Expatria-Technologies/Mods-Accessories/Expatria/Jog2K_Base/6mm_button.SLDPRT

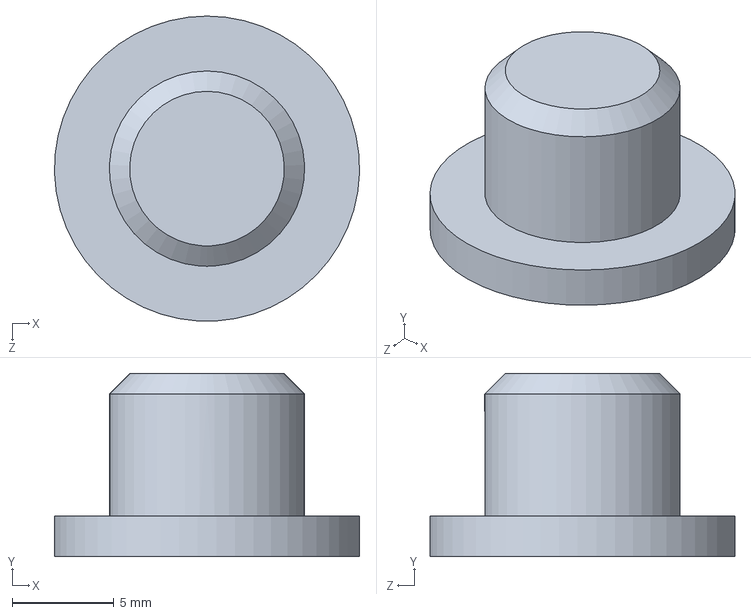
[picture p36: CAD file, 2023-01-20]
Expatria/Jog2K_Base/6mm_button.SLDPRT
15.0 x 9.00 x 15.0 mm
