Expatria-Technologies/Mods-Accessories/Expatria/Jog2K_Deluxe/Buttons/Black/Start Button Cover.stl

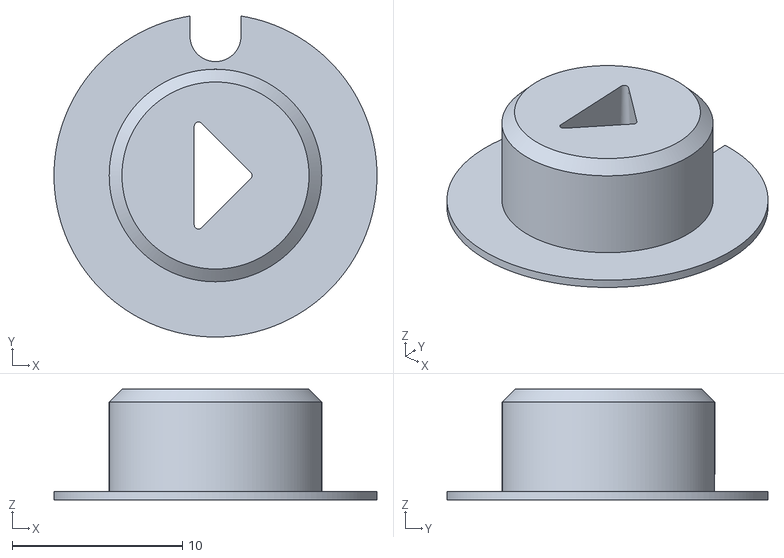
[picture p37: CAD file, 2023-01-20]
Expatria/Jog2K_Deluxe/Buttons/Black/Start Button Cover.stl
19.0 x 18.9 x 6.50
