Expatria-Technologies/Mods-Accessories/Expatria/Jog2K_Deluxe/Buttons/Translucent/Raise Button Lightpipe x2.stl

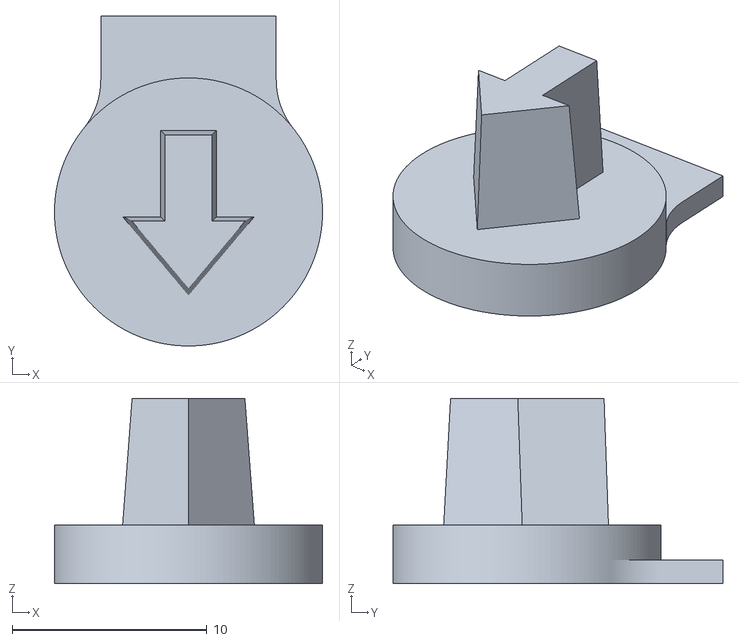
[picture p38: CAD file, 2023-01-20]
Expatria/Jog2K_Deluxe/Buttons/Translucent/Raise Button Lightpipe x2.stl
13.8 x 16.9 x 9.50
