Expatria-Technologies/Mods-Accessories/Expatria/Jog2K_Deluxe/Buttons/White/Mist Button Core.stl

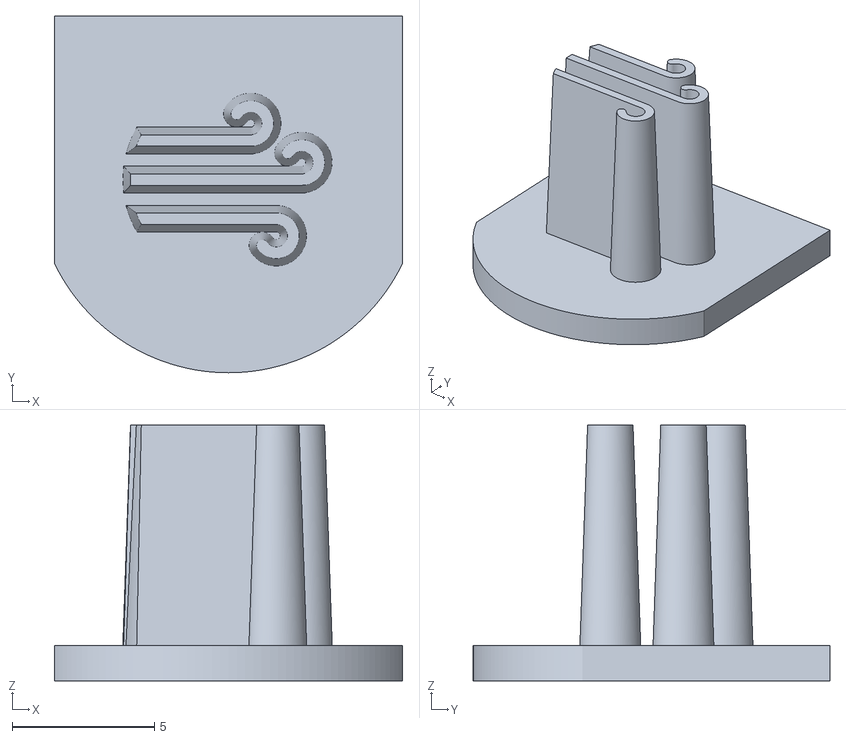
[picture p39: CAD file, 2023-01-20]
Expatria/Jog2K_Deluxe/Buttons/White/Mist Button Core.stl
12.2 x 12.6 x 9.00
