Expatria-Technologies/Mods-Accessories/Expatria/Jog2K_Deluxe/Enclosure/1.3in - Top Cover.STL

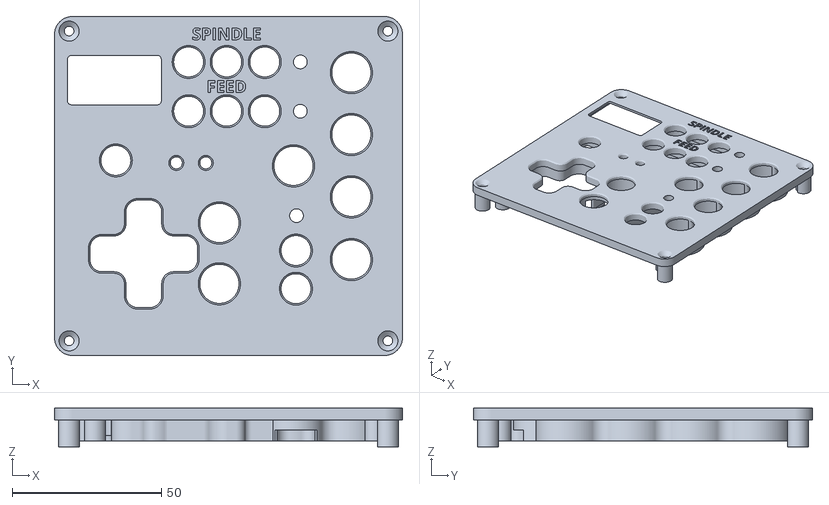
[picture p40: CAD file, 2023-03-23]
Expatria/Jog2K_Deluxe/Enclosure/1.3in - Top Cover.STL
116.5 x 113.5 x 13.0
