Expatria-Technologies/Mods-Accessories/Expatria/Jog2K_Deluxe/Src/0.96in - Jog2K Deluxe Edition.step

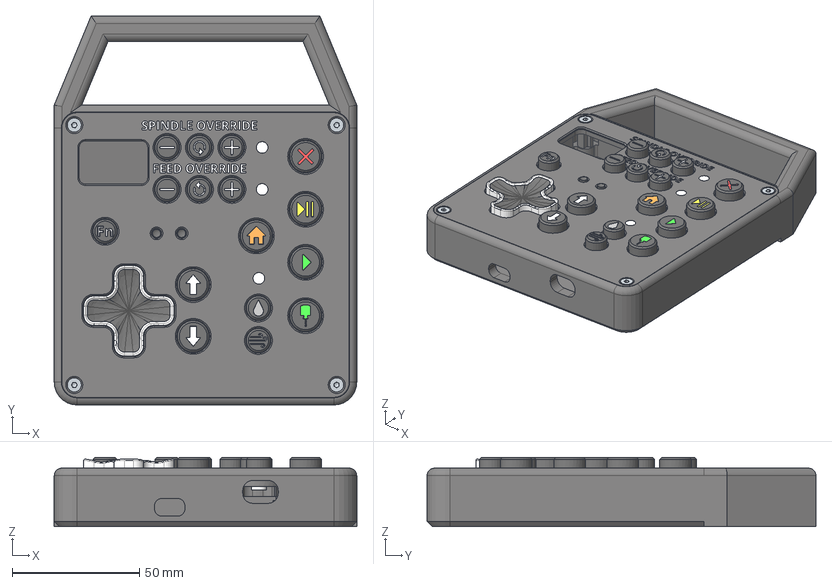
[picture p41: CAD file, 2023-01-22]
Expatria/Jog2K_Deluxe/Src/0.96in - Jog2K Deluxe Edition.step
119.0 x 153.0 x 27.2 mm
Lightpipe x 3
Start Button Cover
Reset Button Core x 2
D-Pad Lower
Spindle Button Lightpipe
Home Button Cover
Hex socket head cap screw M3x0.50 x 6 x 7
Hex socket countersunk head screw M3x0.5 x 16 x 4
Flood Button Cover
Raise Button Lightpipe x 2
Start Button Lightpipe
D-Pad Upper
Plus Button Core x 2
Top Cover
Minus Button Cover x 2
Mist Button Core
Halt Button Lightpipe
Mist Button Cover
Hold Button Lightpipe
Reset Button Cover x 2
Minus Button Core x 2
Plus Button Cover x 2
Fn Button Core
Spindle Button Cover
4mm Button Short x 2
Flood Button Core
Bottom Enclosure
Hold Button Cover
Window
Fn Button Cover
Raise Button Cover x 2
Home Button Lightpipe
Halt Button Cover
