Expatria-Technologies/Mods-Accessories/Expatria/Limit_PCB_Case/Limit Breakout Case Lid.stl

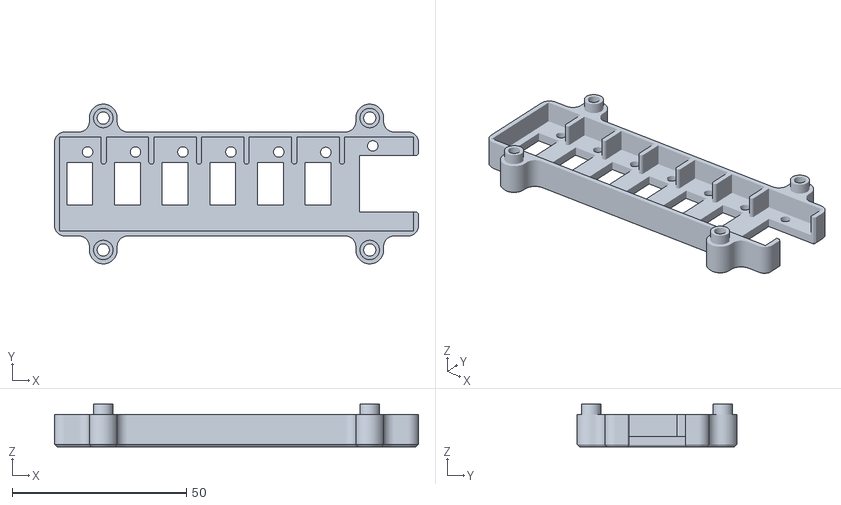
[picture p42: CAD file, 2023-01-20]
Expatria/Limit_PCB_Case/Limit Breakout Case Lid.stl
104.5 x 45.9 x 12.3
