Expatria-Technologies/Mods-Accessories/Community_Submissions/Button_PCB_Case/Button Breakout Case v2.step

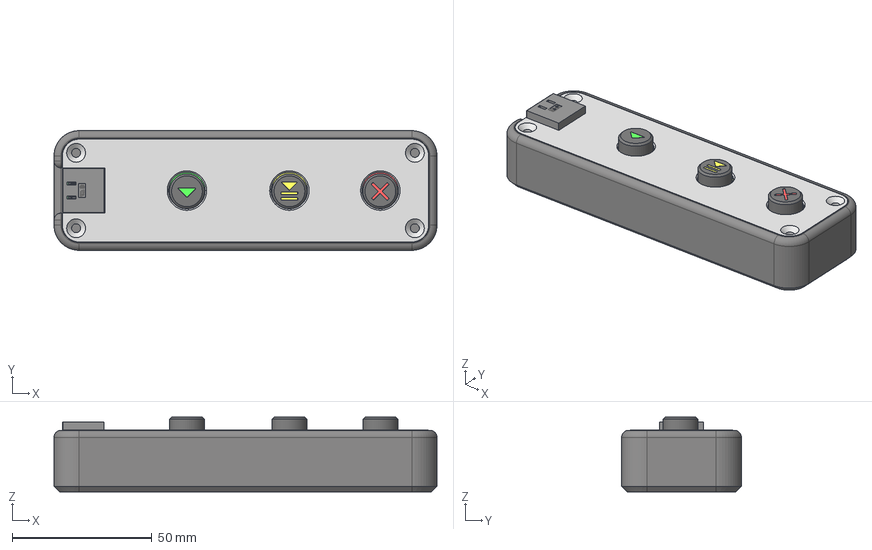
[picture p43: CAD file, 2023-01-20]
Community_Submissions/Button_PCB_Case/Button Breakout Case v2.step
136.9 x 42.8 x 26.7 mm
Conn_Amphenol_RJHSE-5080_eec
c-4-1437565-2-s-3d x 3
User_Library-RES_1609-0603 x 7
User_Library-LED_0603_R_Pocket002 (1) x 4
User_Library-LED_0603_R_Pad004 (1) x 4
User_Library-LED_0603_R_Fillet (1) x 4
User_Library-LED_0603_R_Pocket001 (1) x 4
User_Library-LED_0603_R_Pad (1) x 4
J26 x 4
Top Cover Button Breakout
Bottom Button Breakout Enclosure
Halt Button Cover
Start Button Cover
Start Button Lightpipe
Hold Button Cover
Hold Button Lightpipe
Halt Button Lightpipe
