Expatria-Technologies/Mods-Accessories/Community_Submissions/FDM_Buttons/Black/Home Button Cover.stl

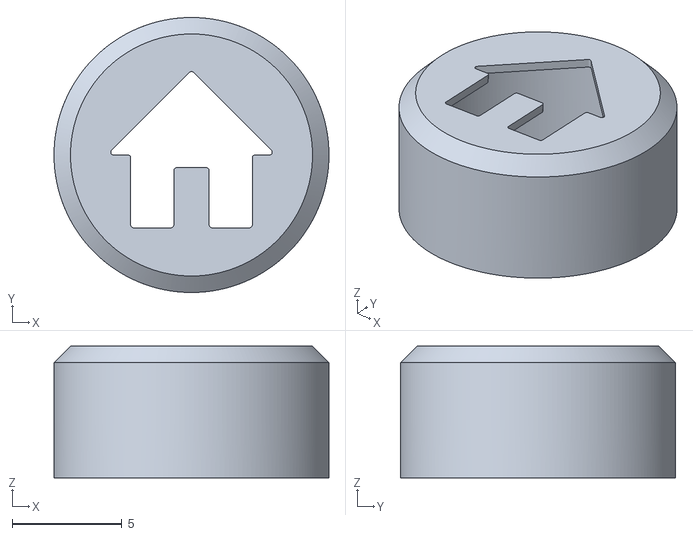
[picture p44: CAD file, 2023-01-20]
Community_Submissions/FDM_Buttons/Black/Home Button Cover.stl
12.5 x 12.5 x 6.00
