Expatria-Technologies/Mods-Accessories/Community_Submissions/FDM_Buttons/Translucent/Z Button Lightpipe 2x.stl

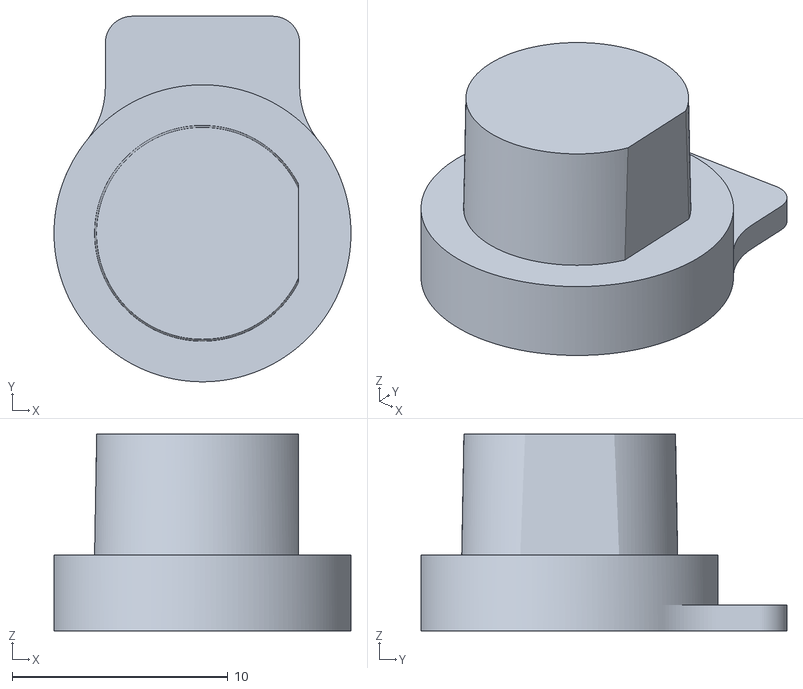
[picture p45: CAD file, 2023-01-20]
Community_Submissions/FDM_Buttons/Translucent/Z Button Lightpipe 2x.stl
13.8 x 16.9 x 9.10
