Expatria-Technologies/Mods-Accessories/Community_Submissions/FDM_Buttons/White/Override Button Core 6x.stl

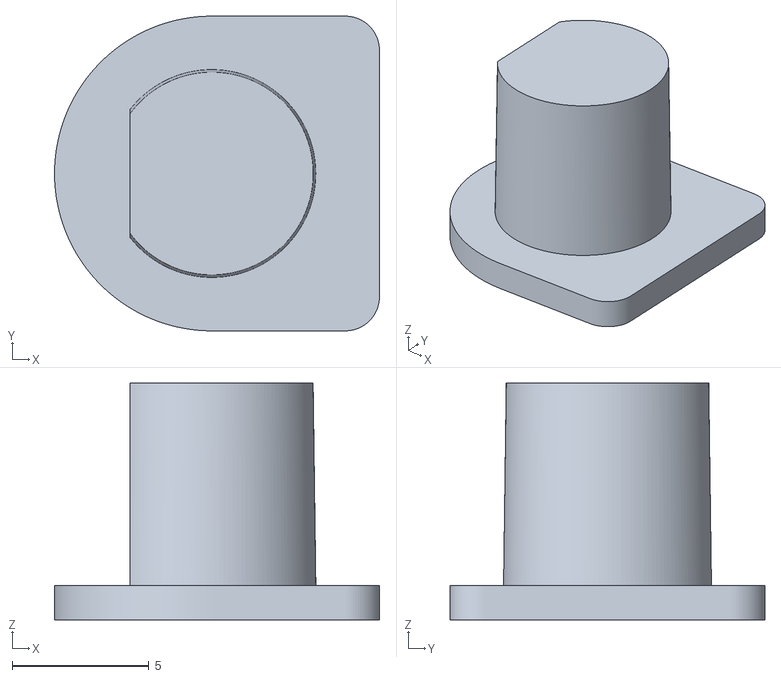
[picture p46: CAD file, 2023-01-20]
Community_Submissions/FDM_Buttons/White/Override Button Core 6x.stl
11.9 x 11.5 x 8.65
