Expatria-Technologies/Mods-Accessories/Community_Submissions/FLEXI_HAL_PI_DIN_RAIL_MOUNT/STL/M2 Spacer 11mm.stl

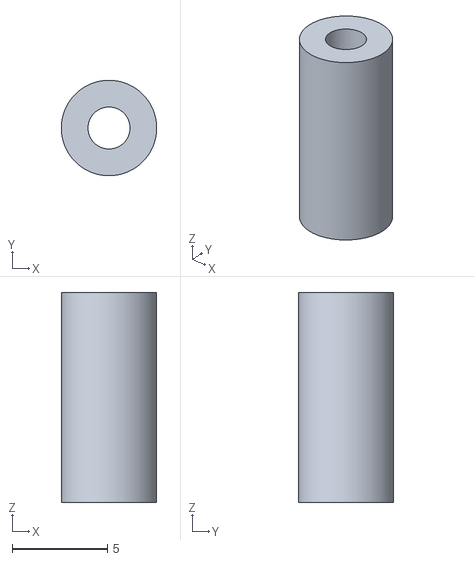
[picture p47: CAD file, 2024-12-16]
Community_Submissions/FLEXI_HAL_PI_DIN_RAIL_MOUNT/STL/M2 Spacer 11mm.stl
5.00 x 5.00 x 11.0
