Expatria-Technologies/Mods-Accessories/Community_Submissions/GH2K_PCB_Mounting_Plate/GH2k or Relay Din Clamp 2x.stl

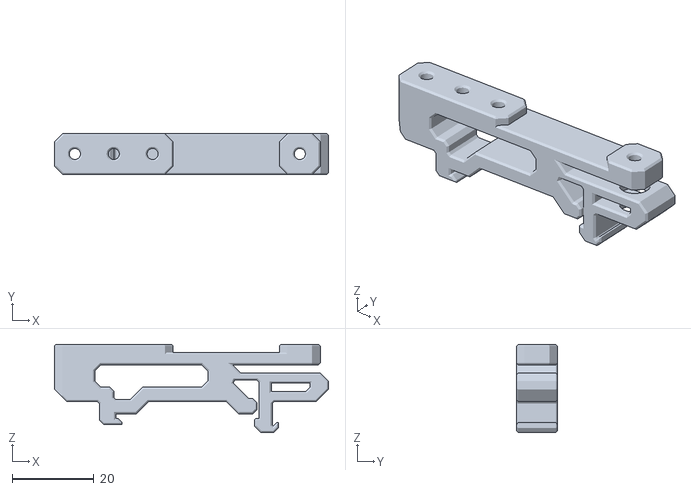
[picture p48: CAD file, 2023-01-20]
Community_Submissions/GH2K_PCB_Mounting_Plate/GH2k or Relay Din Clamp 2x.stl
67.0 x 10.00 x 21.6
