Expatria-Technologies/Mods-Accessories/Community_Submissions/Jog2K_Heavy_Case/CAD/case_front.step

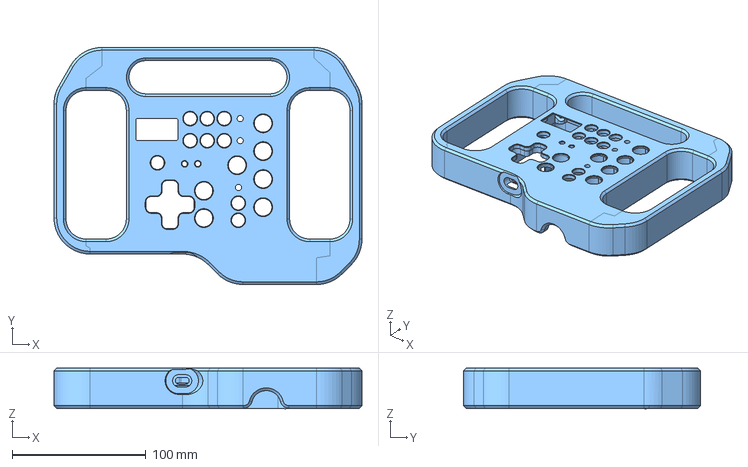
[picture p49: CAD file, 2025-08-29]
Community_Submissions/Jog2K_Heavy_Case/CAD/case_front.step
230.0 x 177.0 x 30.5 mm
