Expatria-Technologies/Mods-Accessories/Community_Submissions/Simplified_High_Vis_Buttons/Coolant.stl

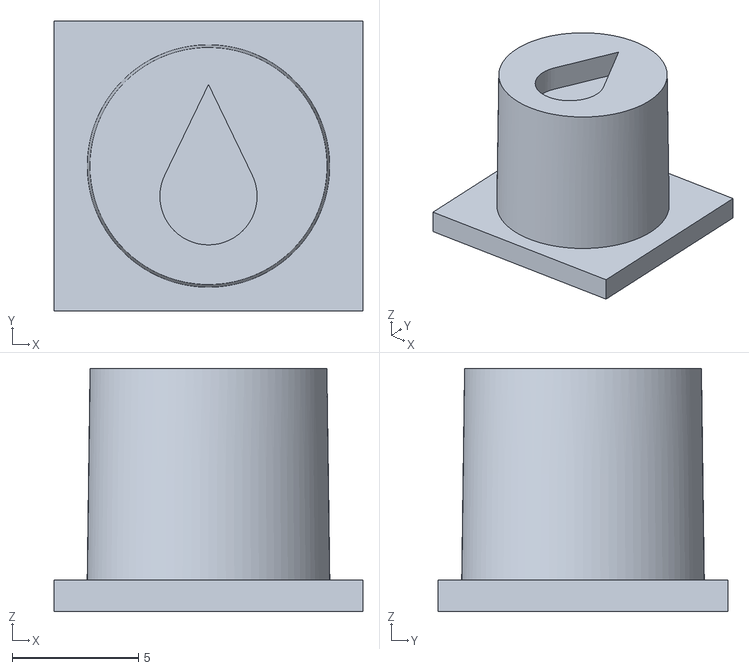
[picture p50: CAD file, 2023-01-22]
Community_Submissions/Simplified_High_Vis_Buttons/Coolant.stl
12.2 x 11.5 x 9.65
