Expatria-Technologies/Mods-Accessories/Expatria/Encoder_MK2_Case/encoderMK2_Enclosure_bottom.STEP

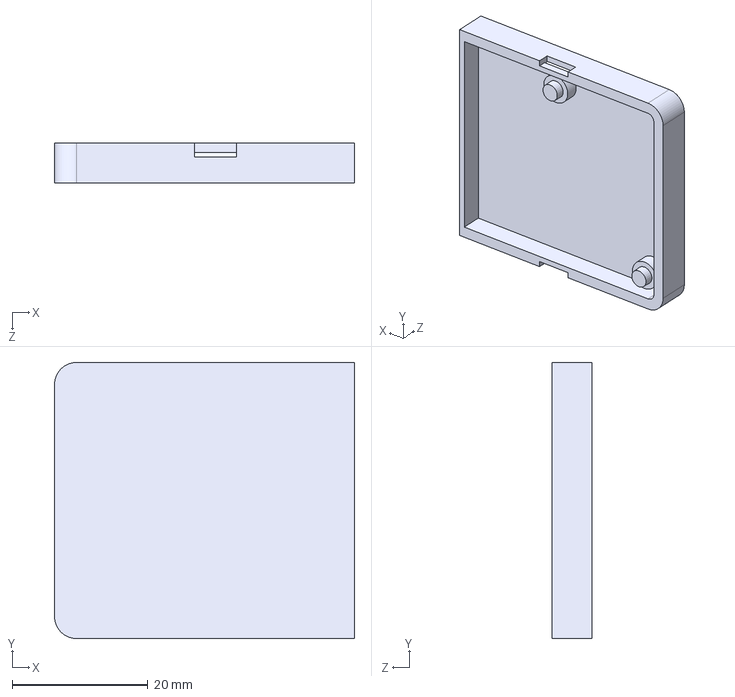
[picture p51: CAD file, 2024-12-16]
Expatria/Encoder_MK2_Case/encoderMK2_Enclosure_bottom.STEP
44.1 x 40.6 x 5.90 mm
