Expatria-Technologies/Mods-Accessories/Expatria/Jog2K_Base/jog_bottom_box_slim.SLDPRT

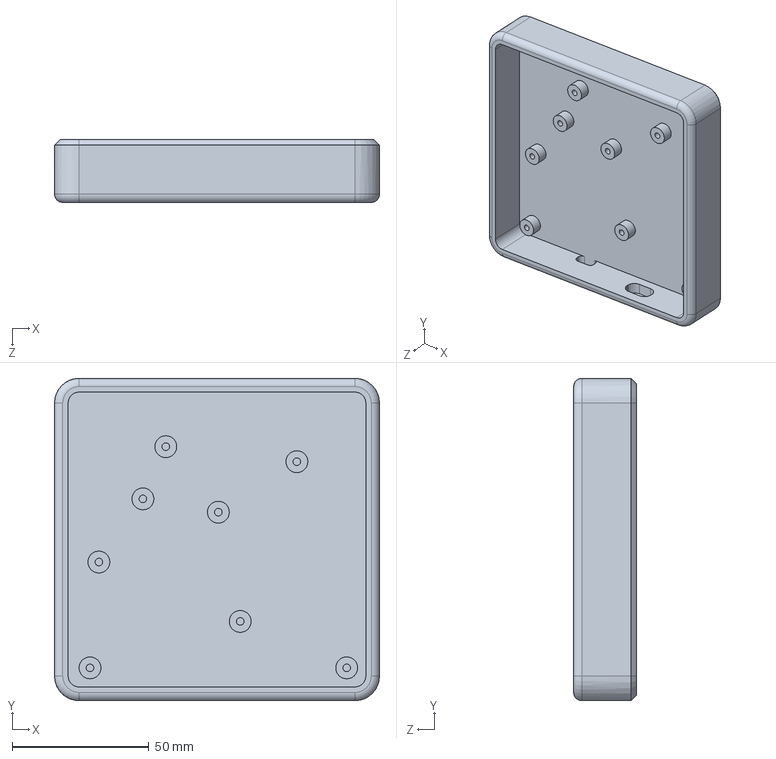
[picture p52: CAD file, 2023-01-20]
Expatria/Jog2K_Base/jog_bottom_box_slim.SLDPRT
119.0 x 118.0 x 23.0 mm
