Expatria-Technologies/Mods-Accessories/Expatria/Jog2K_Deluxe/Buttons/White/Reset Button Core x2.stl

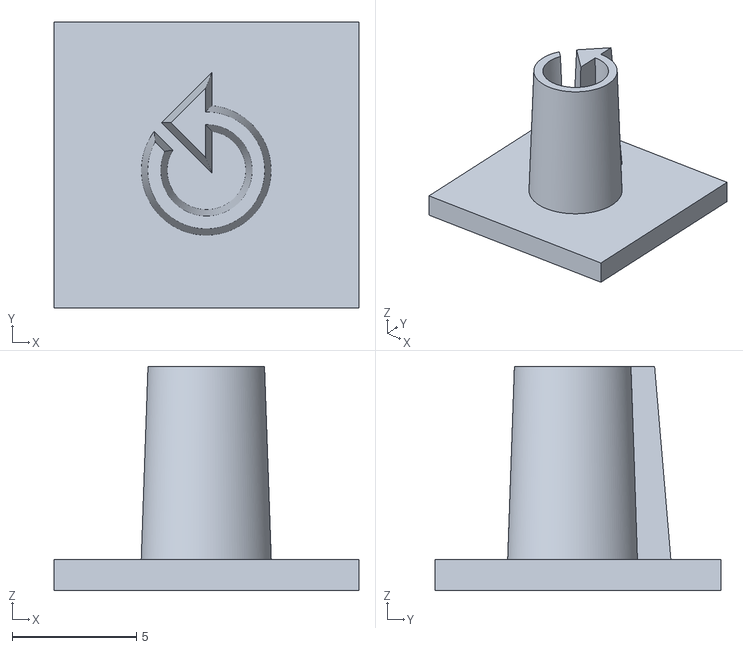
[picture p55: CAD file, 2023-01-20]
Expatria/Jog2K_Deluxe/Buttons/White/Reset Button Core x2.stl
12.2 x 11.5 x 9.00
