Expatria-Technologies/Mods-Accessories/Expatria/Jog2K_Deluxe/Enclosure/Slim - 1.3in Display Insert.stl

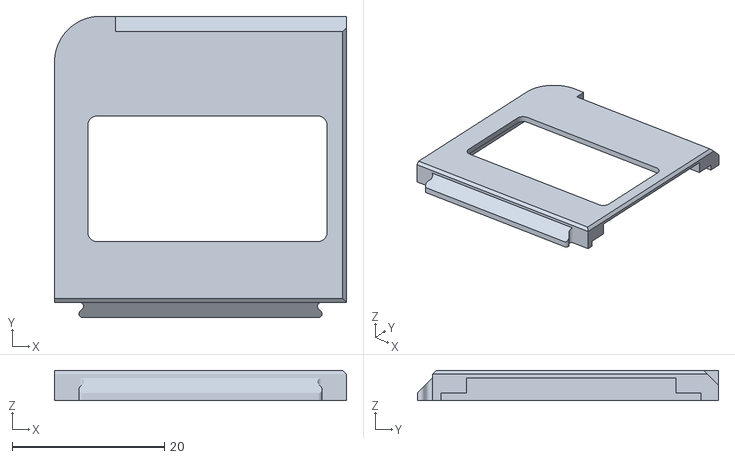
[picture p56: CAD file, 2023-02-04]
Expatria/Jog2K_Deluxe/Enclosure/Slim - 1.3in Display Insert.stl
38.3 x 39.5 x 4.00
