Expatria-Technologies/Mods-Accessories/Expatria/Limit_PCB_Case/Limit Breakout Case Base.stl

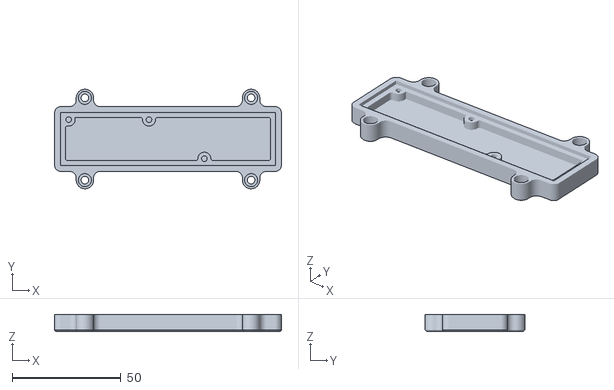
[picture p57: CAD file, 2023-01-20]
Expatria/Limit_PCB_Case/Limit Breakout Case Base.stl
104.5 x 45.9 x 8.00
