Expatria-Technologies/Mods-Accessories/Community_Submissions/Button_PCB_Case/Button PCB Case Cover.stl

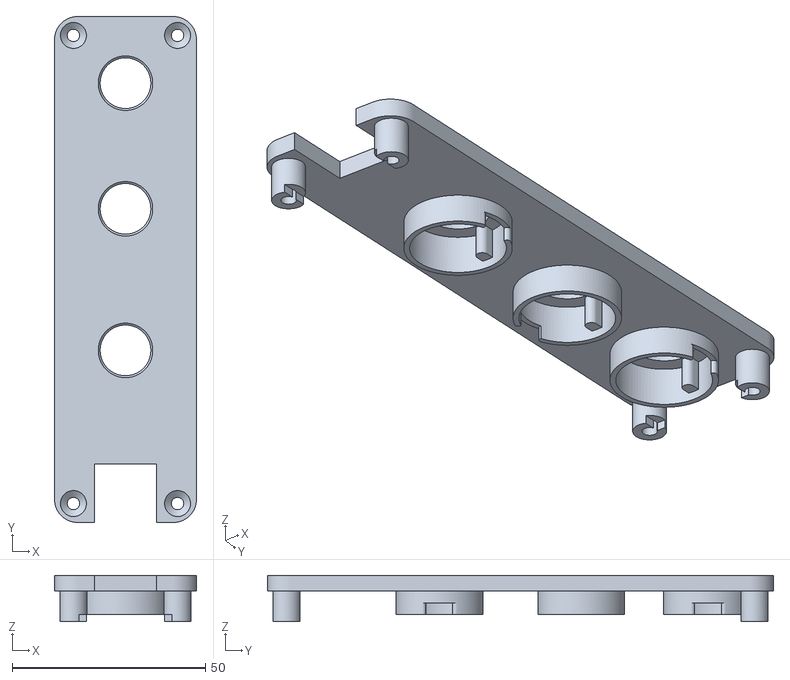
[picture p58: CAD file, 2023-01-20]
Community_Submissions/Button_PCB_Case/Button PCB Case Cover.stl
36.8 x 130.9 x 12.0
