Expatria-Technologies/Mods-Accessories/Community_Submissions/Button_PCB_Case/FDM Buttons/Black/Hold Button Cover.stl

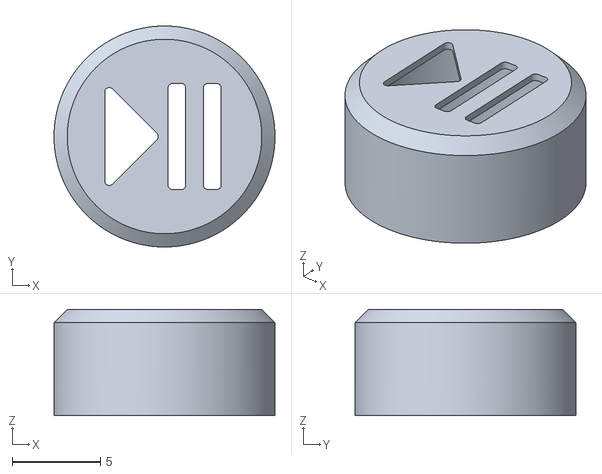
[picture p59: CAD file, 2023-01-20]
Community_Submissions/Button_PCB_Case/FDM Buttons/Black/Hold Button Cover.stl
12.5 x 12.5 x 6.00
