Expatria-Technologies/Mods-Accessories/Community_Submissions/FDM_Buttons/Black/Raise Button Cover 2x.stl

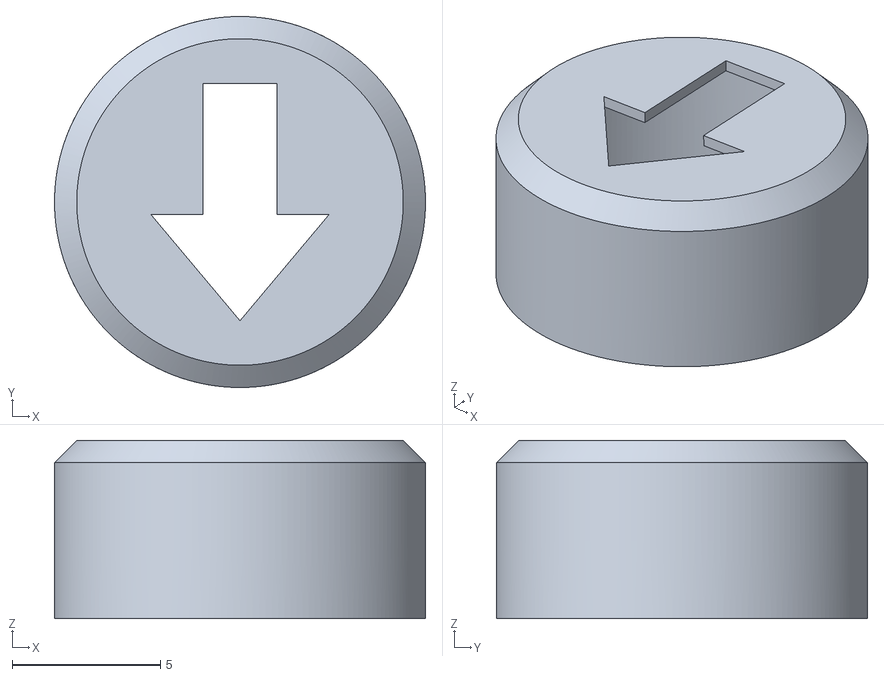
[picture p60: CAD file, 2023-01-20]
Community_Submissions/FDM_Buttons/Black/Raise Button Cover 2x.stl
12.5 x 12.5 x 6.00
