Expatria-Technologies/Mods-Accessories/Community_Submissions/FDM_Buttons/Translucent/Lightpipe x3.stl

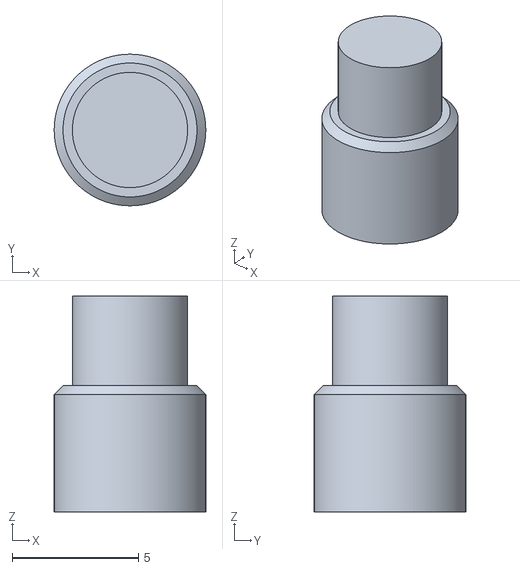
[picture p61: CAD file, 2023-01-20]
Community_Submissions/FDM_Buttons/Translucent/Lightpipe x3.stl
6.00 x 6.00 x 8.55
