Expatria-Technologies/Mods-Accessories/Community_Submissions/FLEXI_HAL_PI_DIN_RAIL_MOUNT/STL/DIN_Clip.stl

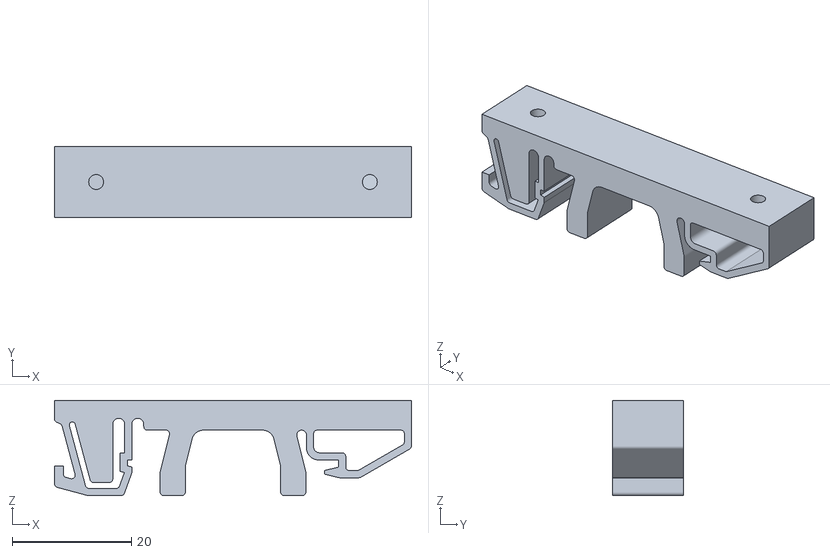
[picture p62: CAD file, 2023-01-20]
Community_Submissions/FLEXI_HAL_PI_DIN_RAIL_MOUNT/STL/DIN_Clip.stl
60.0 x 12.0 x 16.0
