Expatria-Technologies/Mods-Accessories/Community_Submissions/GH2K_PCB_Mounting_Plate/GH2K DIN Mounting Plate.stl

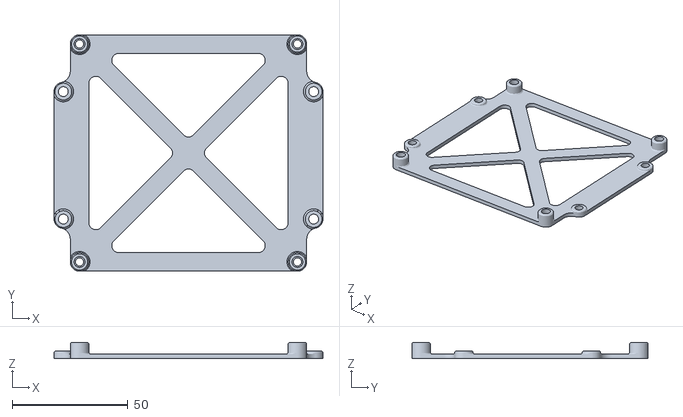
[picture p63: CAD file, 2023-01-20]
Community_Submissions/GH2K_PCB_Mounting_Plate/GH2K DIN Mounting Plate.stl
116.1 x 102.0 x 7.00
