Expatria-Technologies/Mods-Accessories/Community_Submissions/Simplified_High_Vis_Buttons/PlusOverrideX2.stl

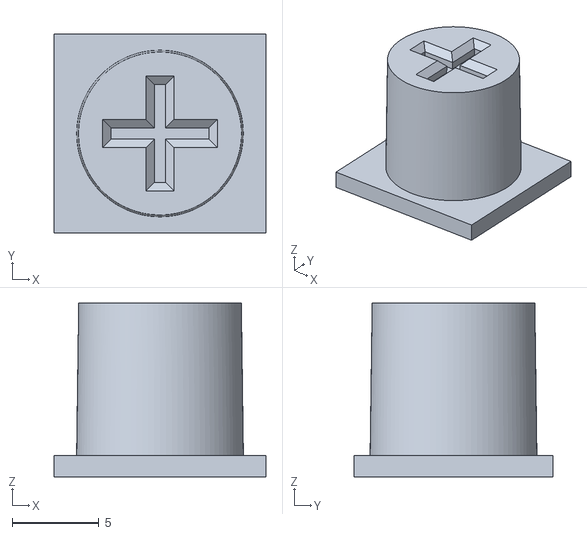
[picture p64: CAD file, 2023-01-22]
Community_Submissions/Simplified_High_Vis_Buttons/PlusOverrideX2.stl
12.2 x 11.5 x 10.0
