Expatria-Technologies/Mods-Accessories/Expatria/Jog2K_Deluxe/Buttons/Black/Mist Button Cover.stl

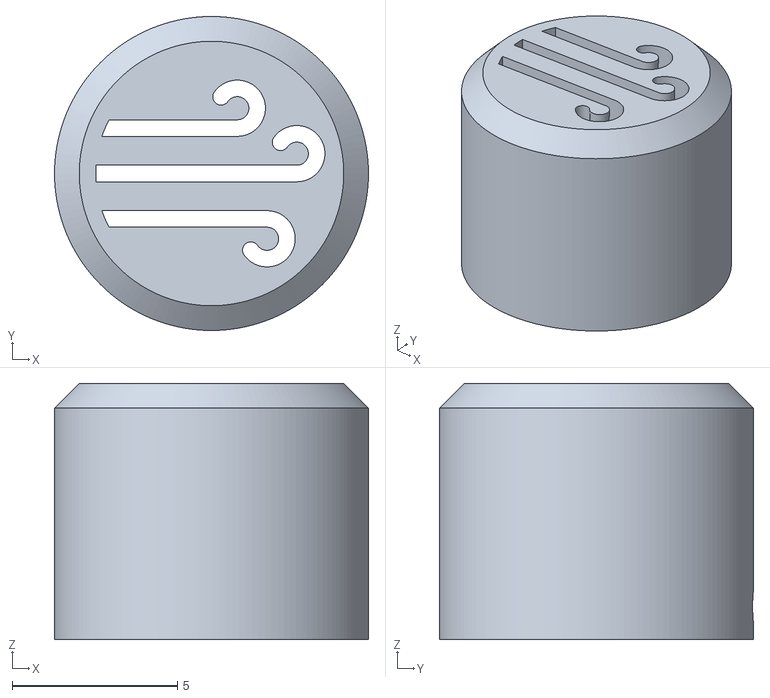
[picture p65: CAD file, 2023-01-20]
Expatria/Jog2K_Deluxe/Buttons/Black/Mist Button Cover.stl
9.50 x 9.50 x 7.75
