Expatria-Technologies/Mods-Accessories/Expatria/Jog2K_Deluxe/Enclosure/Slim - Blank Display Insert.stl

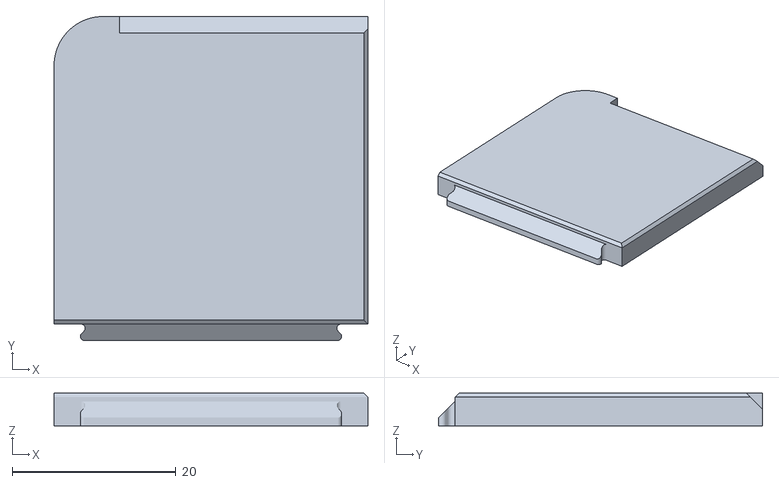
[picture p67: CAD file, 2023-02-04]
Expatria/Jog2K_Deluxe/Enclosure/Slim - Blank Display Insert.stl
38.3 x 39.5 x 4.00
