Expatria-Technologies/Mods-Accessories/Expatria/Limit_PCB_Case/Limit Breakout Lightpipe x7.stl

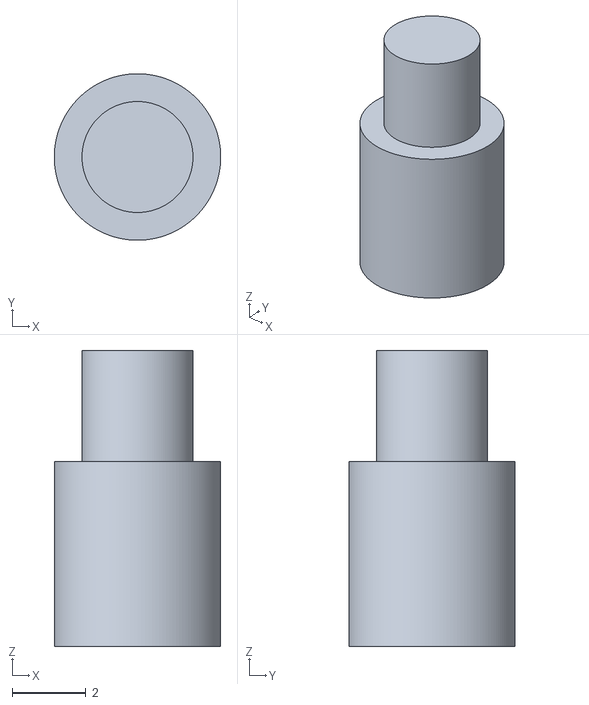
[picture p68: CAD file, 2023-01-20]
Expatria/Limit_PCB_Case/Limit Breakout Lightpipe x7.stl
4.50 x 4.50 x 8.00
