Expatria-Technologies/Mods-Accessories/Community_Submissions/FDM_Buttons/Black/Reset Button Cover 2x.stl

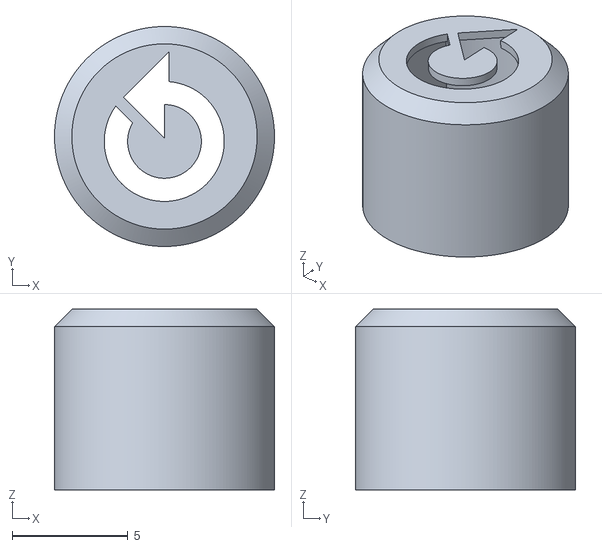
[picture p69: CAD file, 2023-01-20]
Community_Submissions/FDM_Buttons/Black/Reset Button Cover 2x.stl
9.50 x 9.50 x 7.80
