Expatria-Technologies/Mods-Accessories/Community_Submissions/Simplified_High_Vis_Buttons/Wind.stl

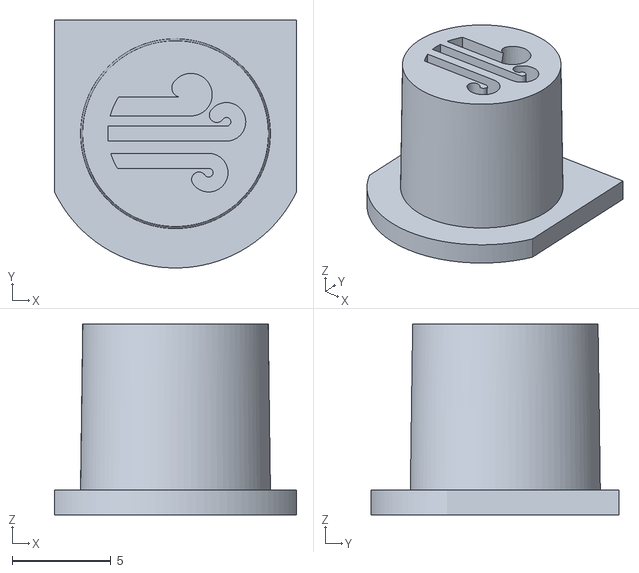
[picture p70: CAD file, 2023-01-22]
Community_Submissions/Simplified_High_Vis_Buttons/Wind.stl
12.2 x 12.5 x 9.65
