Expatria-Technologies/Mods-Accessories/Expatria/Jog2K_Base/10mm_button.SLDPRT

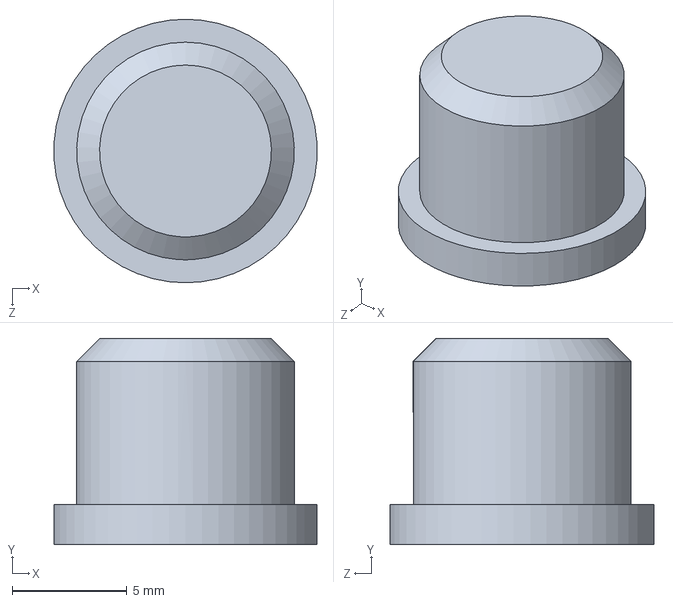
[picture p71: CAD file, 2023-01-20]
Expatria/Jog2K_Base/10mm_button.SLDPRT
11.5 x 9.00 x 11.5 mm
