Expatria-Technologies/Mods-Accessories/Expatria/Jog2K_Deluxe/Buttons/White/Minus Button Core x2.stl

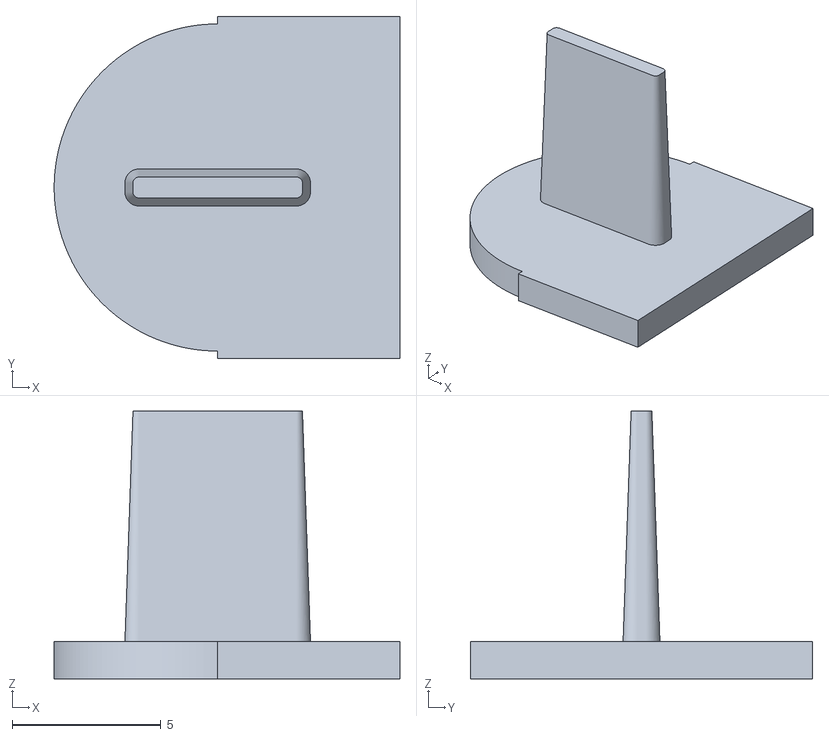
[picture p74: CAD file, 2023-01-20]
Expatria/Jog2K_Deluxe/Buttons/White/Minus Button Core x2.stl
11.6 x 11.5 x 9.00
