Expatria-Technologies/Mods-Accessories/Expatria/Jog2K_Deluxe/Enclosure/Slim - Top Cover.stl

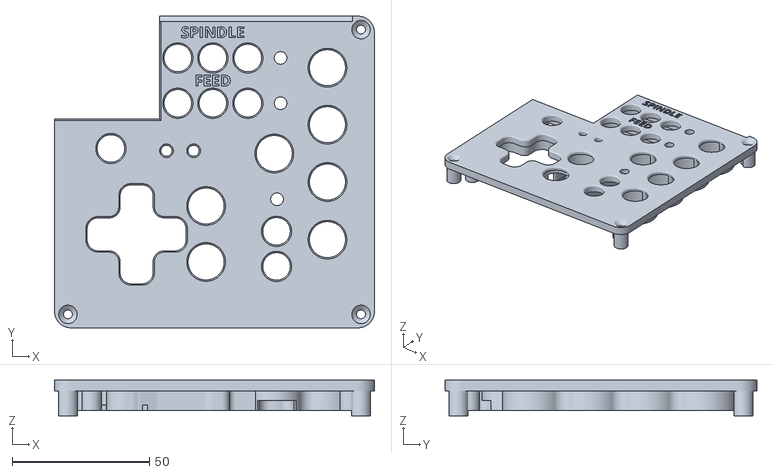
[picture p75: CAD file, 2023-02-04]
Expatria/Jog2K_Deluxe/Enclosure/Slim - Top Cover.stl
116.5 x 113.5 x 13.0
