Expatria-Technologies/Mods-Accessories/Community_Submissions/Simplified_High_Vis_Buttons/FnButton.stl

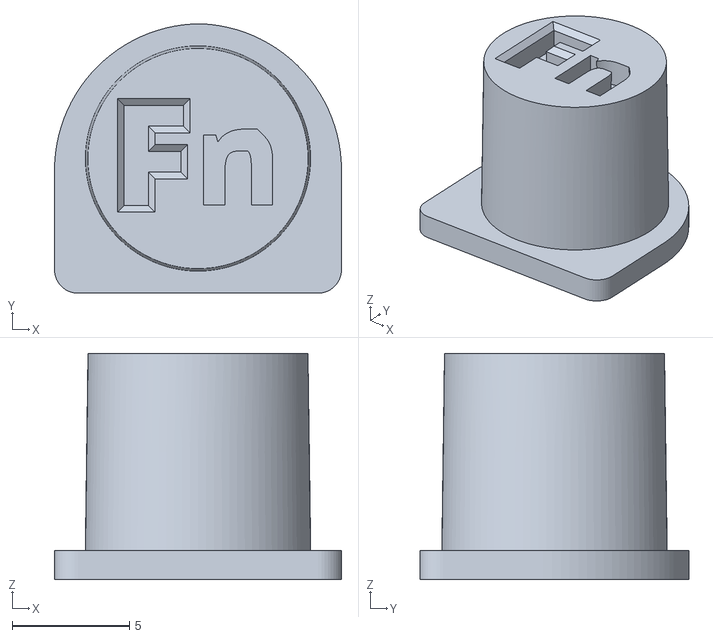
[picture p76: CAD file, 2023-01-22]
Community_Submissions/Simplified_High_Vis_Buttons/FnButton.stl
12.2 x 11.5 x 9.65
