Expatria-Technologies/Mods-Accessories/Expatria/Jog2K_Base/TopCover.SLDPRT

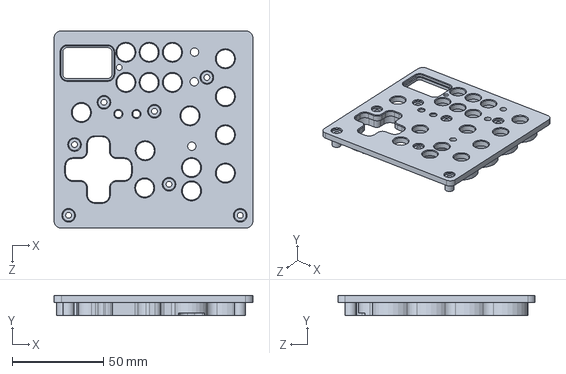
[picture p77: CAD file, 2023-01-20]
Expatria/Jog2K_Base/TopCover.SLDPRT
109.0 x 11.1 x 108.0 mm
