Expatria-Technologies/Mods-Accessories/Expatria/Jog2K_Deluxe/Buttons/Black/Reset Button Cover x2.stl

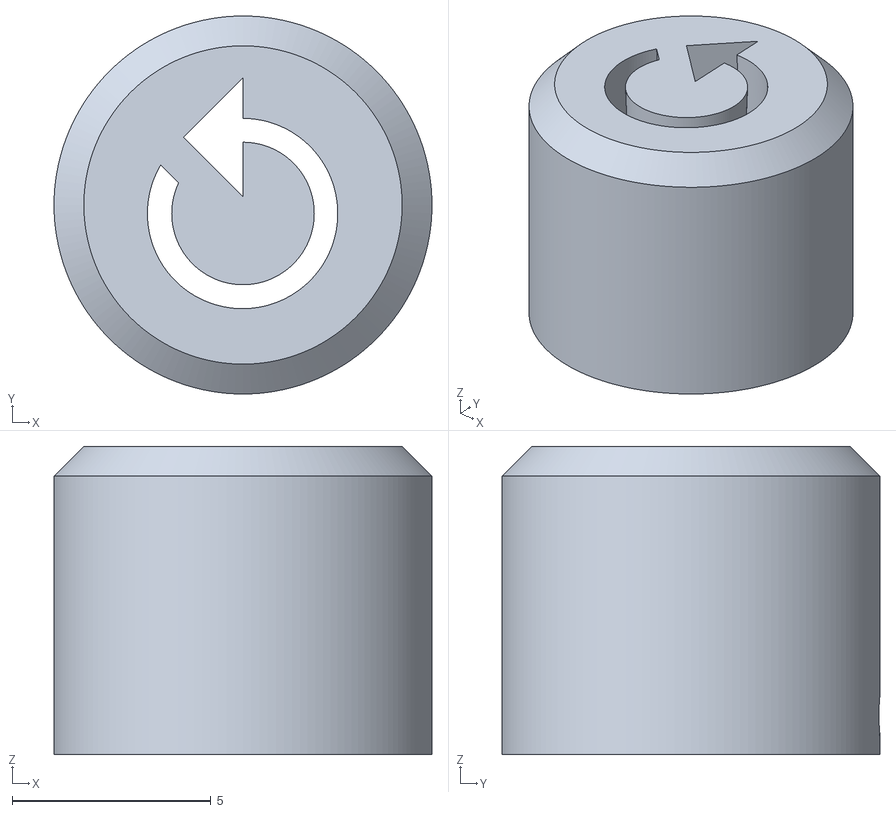
[picture p78: CAD file, 2023-01-20]
Expatria/Jog2K_Deluxe/Buttons/Black/Reset Button Cover x2.stl
9.50 x 9.50 x 7.75
