Expatria-Technologies/Mods-Accessories/Expatria/Jog2K_Deluxe/Buttons/Translucent/Hold Button Lightpipe.stl

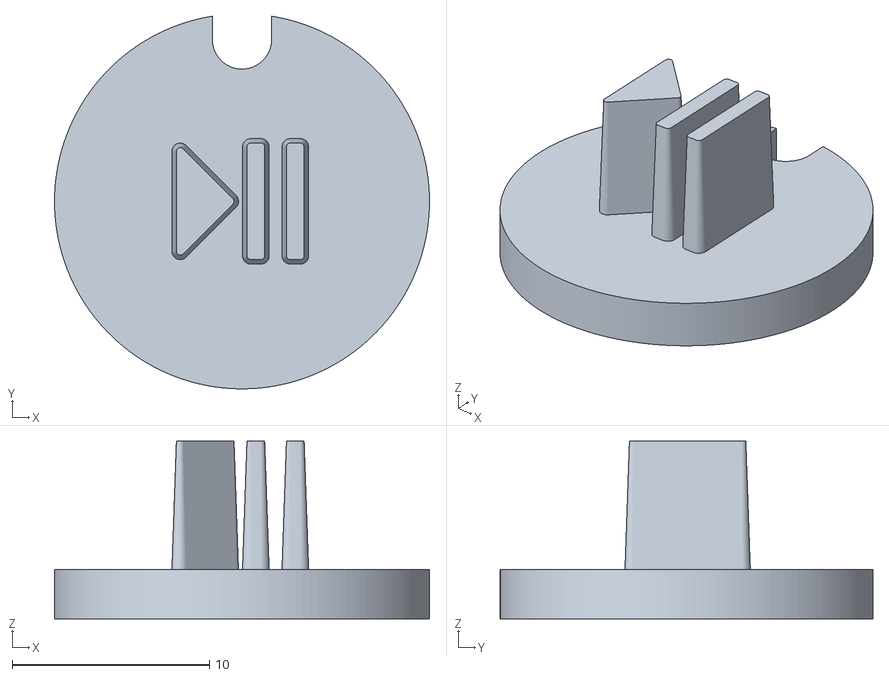
[picture p79: CAD file, 2023-01-20]
Expatria/Jog2K_Deluxe/Buttons/Translucent/Hold Button Lightpipe.stl
19.0 x 18.9 x 9.00
