Expatria-Technologies/Mods-Accessories/Expatria/Jog2K_Deluxe/Enclosure/Slim - Bottom Enclosure.stl

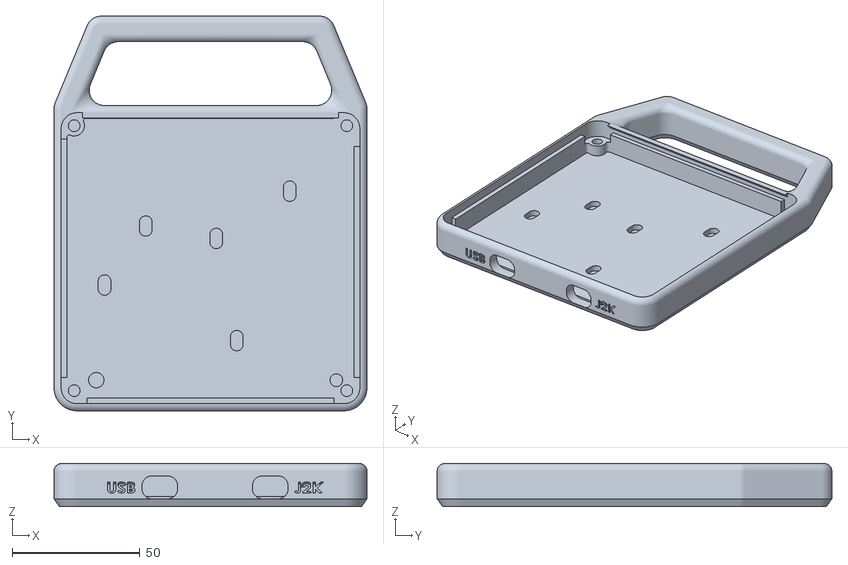
[picture p81: CAD file, 2023-02-04]
Expatria/Jog2K_Deluxe/Enclosure/Slim - Bottom Enclosure.stl
122.6 x 154.5 x 16.9
