Expatria-Technologies/Mods-Accessories/Community_Submissions/FDM_Buttons/Black/MicroUSBFiller.stl

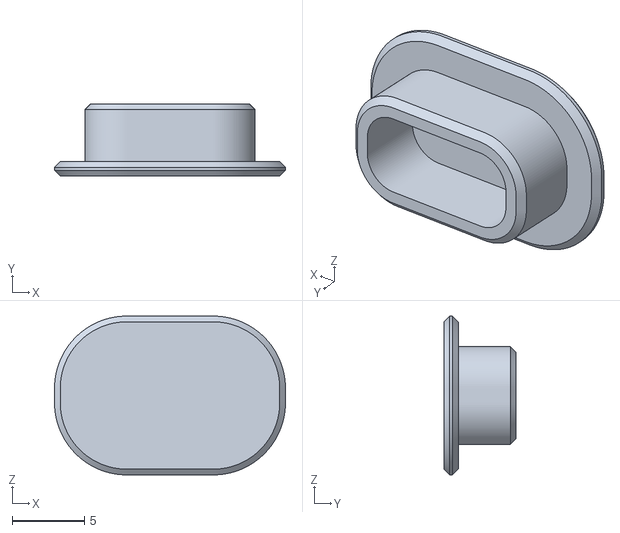
[picture p82: CAD file, 2023-01-20]
Community_Submissions/FDM_Buttons/Black/MicroUSBFiller.stl
16.0 x 5.00 x 11.0
