Expatria-Technologies/Mods-Accessories/Community_Submissions/Simplified_High_Vis_Buttons/MinusOverrideX2.stl

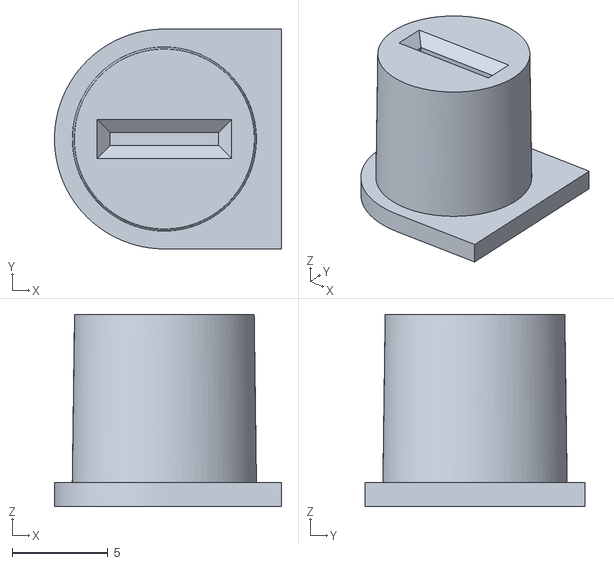
[picture p83: CAD file, 2023-01-22]
Community_Submissions/Simplified_High_Vis_Buttons/MinusOverrideX2.stl
11.9 x 11.5 x 10.0
