Expatria-Technologies/Mods-Accessories/Expatria/Jog2K_Deluxe/Buttons/Black/D-Pad Upper.stl

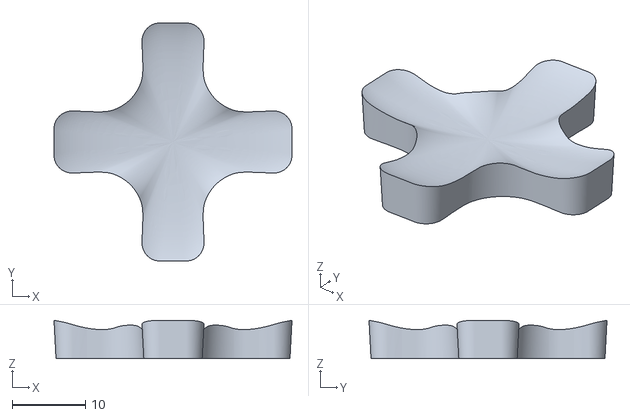
[picture p84: CAD file, 2023-01-20]
Expatria/Jog2K_Deluxe/Buttons/Black/D-Pad Upper.stl
32.5 x 32.5 x 5.19
