Expatria-Technologies/Mods-Accessories/Expatria/Jog2K_Deluxe/Buttons/Translucent/Start Button Lightpipe.stl

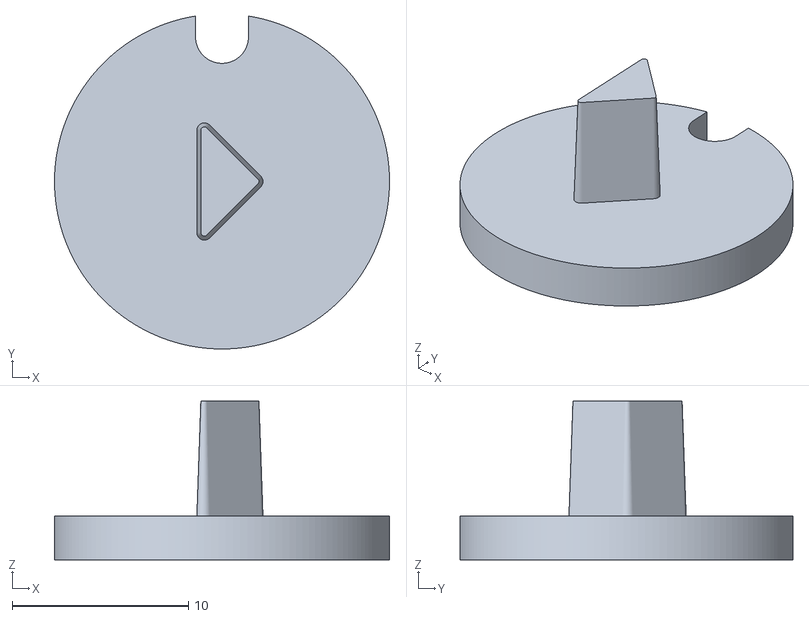
[picture p85: CAD file, 2023-01-20]
Expatria/Jog2K_Deluxe/Buttons/Translucent/Start Button Lightpipe.stl
19.0 x 18.9 x 9.00
