Expatria-Technologies/Mods-Accessories/Expatria/Jog2K_Deluxe/Buttons/White/Fn Button Core.stl

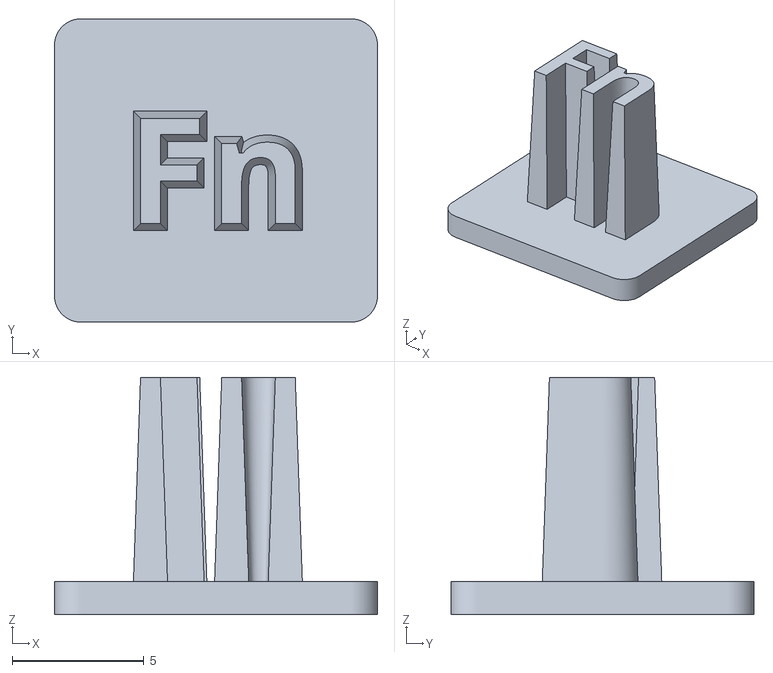
[picture p86: CAD file, 2023-01-20]
Expatria/Jog2K_Deluxe/Buttons/White/Fn Button Core.stl
12.2 x 11.5 x 9.00
