Expatria-Technologies/Mods-Accessories/Expatria/Jog2K_Deluxe/Enclosure/0.96in - Top Cover.stl

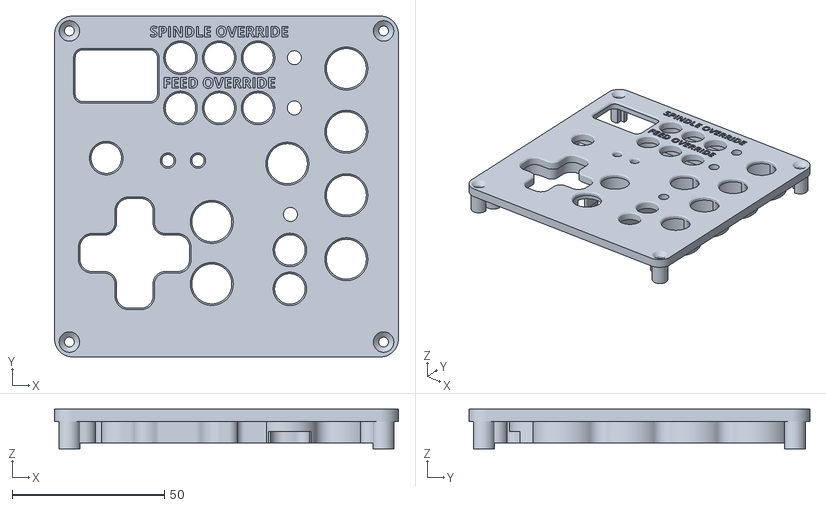
[picture p87: CAD file, 2023-01-22]
Expatria/Jog2K_Deluxe/Enclosure/0.96in - Top Cover.stl
113.0 x 112.0 x 13.0
