Expatria-Technologies/Mods-Accessories/Expatria/Jog2K_Base/lightpipe_x3.STL

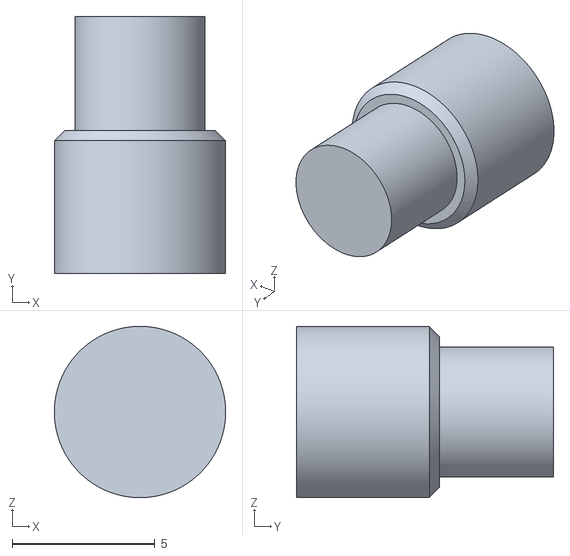
[picture p88: CAD file, 2023-01-20]
Expatria/Jog2K_Base/lightpipe_x3.STL
6.00 x 9.00 x 6.00
