Expatria-Technologies/Mods-Accessories/Expatria/Jog2K_Deluxe/Enclosure/1.3in - Bottom Enclosure.stl

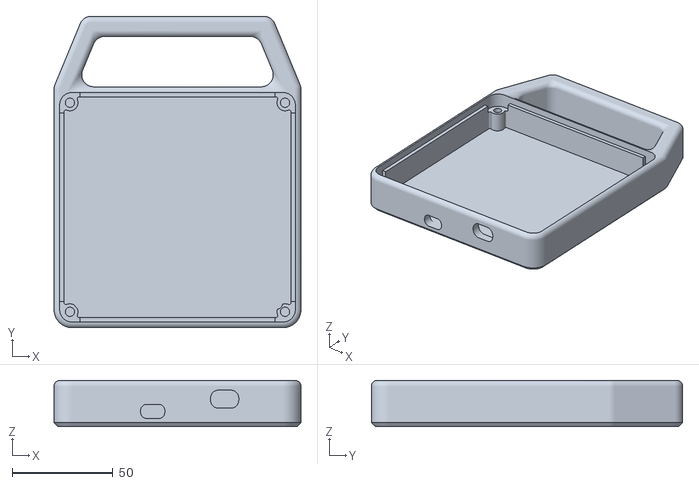
[picture p91: CAD file, 2023-01-20]
Expatria/Jog2K_Deluxe/Enclosure/1.3in - Bottom Enclosure.stl
122.6 x 154.5 x 23.0
