Expatria-Technologies/Mods-Accessories/Community_Submissions/FDM_Buttons/Black/Minus Button Cover 2X.stl

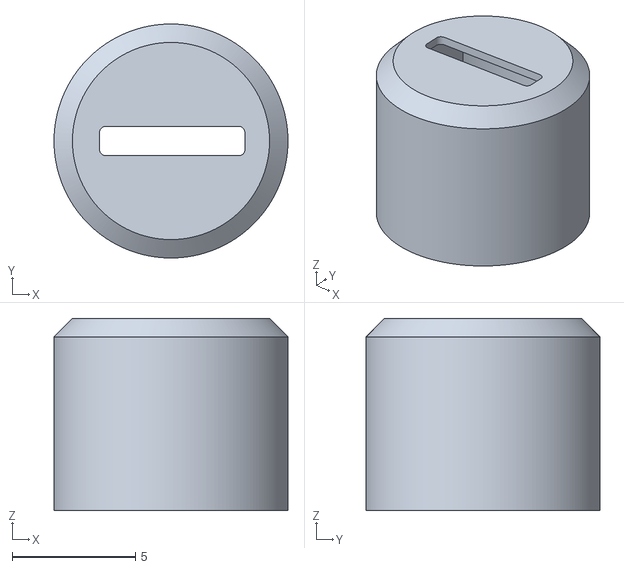
[picture p92: CAD file, 2023-01-20]
Community_Submissions/FDM_Buttons/Black/Minus Button Cover 2X.stl
9.50 x 9.50 x 7.80
