Expatria-Technologies/Mods-Accessories/Expatria/Jog2K_Base/dpad.SLDPRT

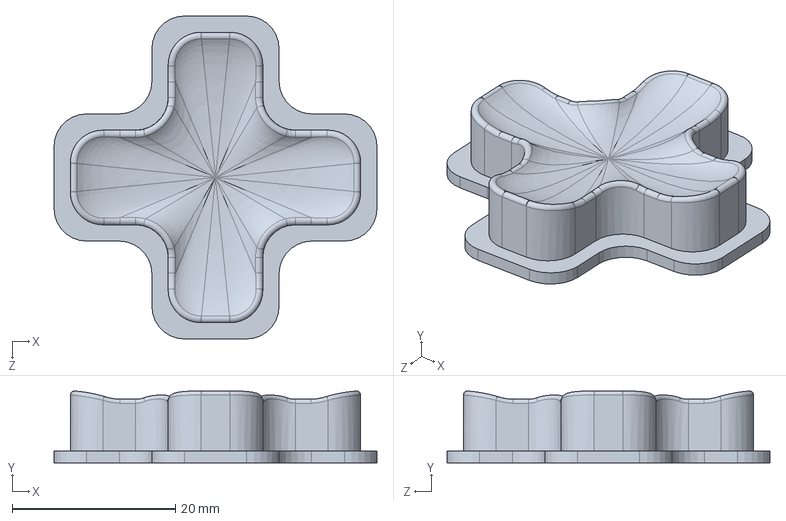
[picture p93: CAD file, 2023-01-20]
Expatria/Jog2K_Base/dpad.SLDPRT
39.6 x 8.83 x 39.6 mm
