Expatria-Technologies/Mods-Accessories/Expatria/Jog2K_Deluxe/Enclosure/0.96in - Window.stl

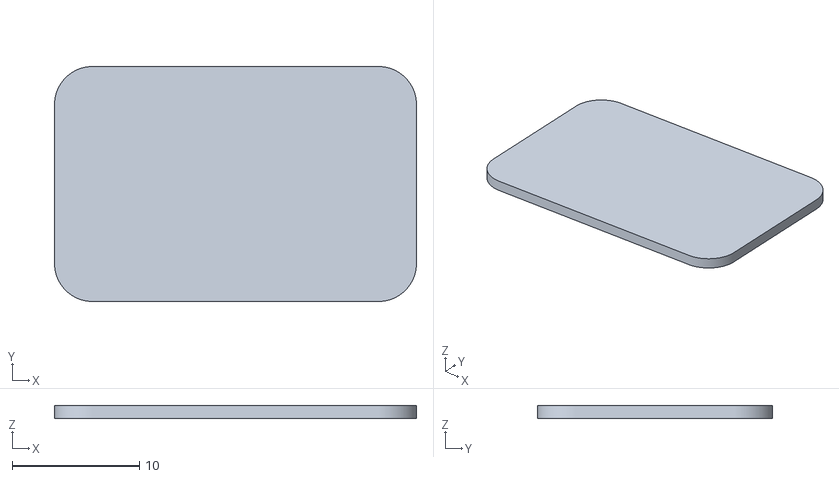
[picture p94: CAD file, 2023-01-20]
Expatria/Jog2K_Deluxe/Enclosure/0.96in - Window.stl
28.5 x 18.5 x 1.00
