Expatria-Technologies/Mods-Accessories/Community_Submissions/FDM_Buttons/Black/Flood Button Cover.stl

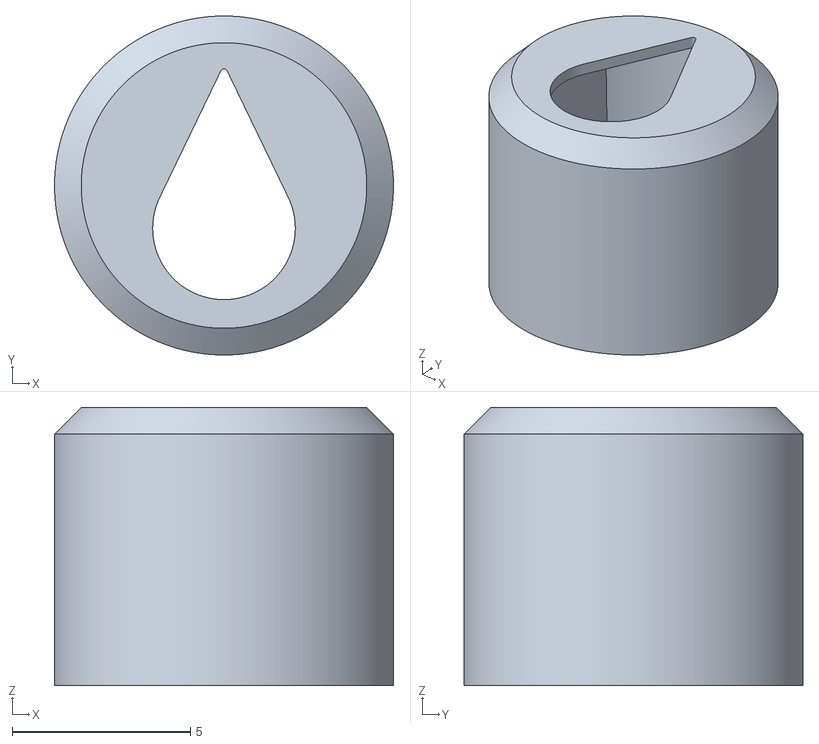
[picture p95: CAD file, 2023-01-20]
Community_Submissions/FDM_Buttons/Black/Flood Button Cover.stl
9.50 x 9.50 x 7.80
