Expatria-Technologies/Mods-Accessories/Expatria/Jog2K_Base/jog_bottom_box.SLDPRT

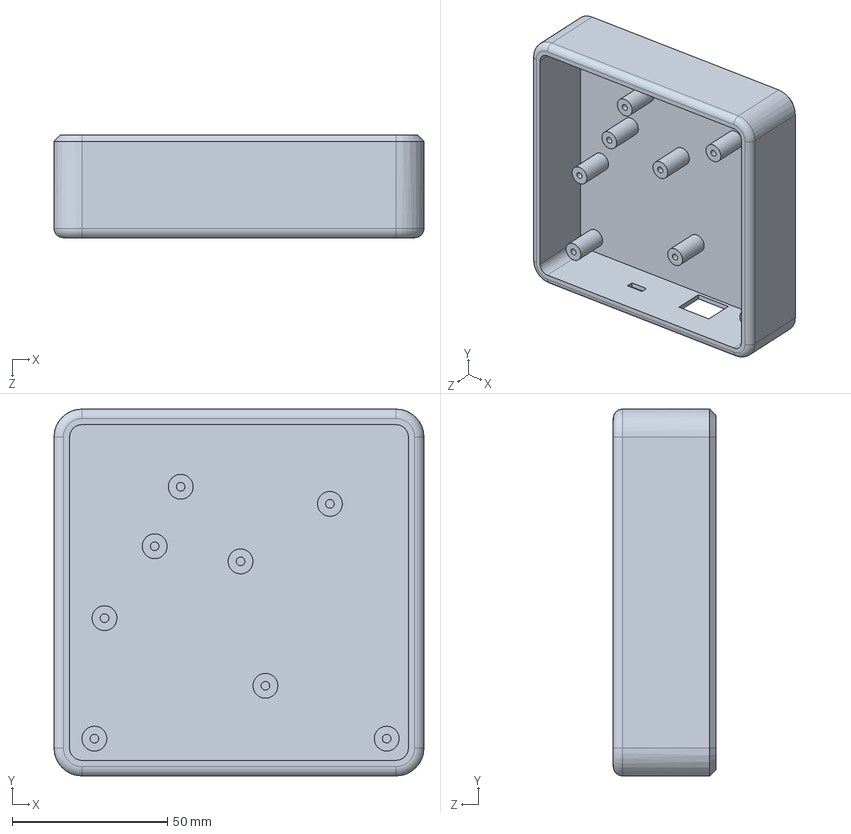
[picture p96: CAD file, 2023-01-20]
Expatria/Jog2K_Base/jog_bottom_box.SLDPRT
119.0 x 118.0 x 33.0 mm
