Expatria-Technologies/Mods-Accessories/Expatria/Jog2K_Deluxe/Enclosure/0.96in - Bottom Enclosure.stl

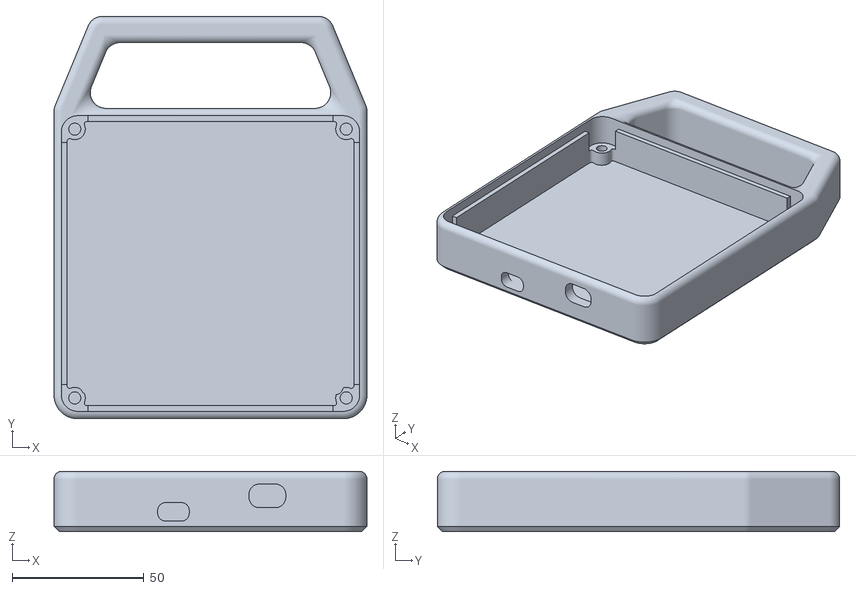
[picture p97: CAD file, 2023-01-20]
Expatria/Jog2K_Deluxe/Enclosure/0.96in - Bottom Enclosure.stl
119.0 x 153.0 x 23.0
