Expatria-Technologies/Mods-Accessories/Expatria/Jog2K_Deluxe/Enclosure/1.3in - Display Retainer.stl

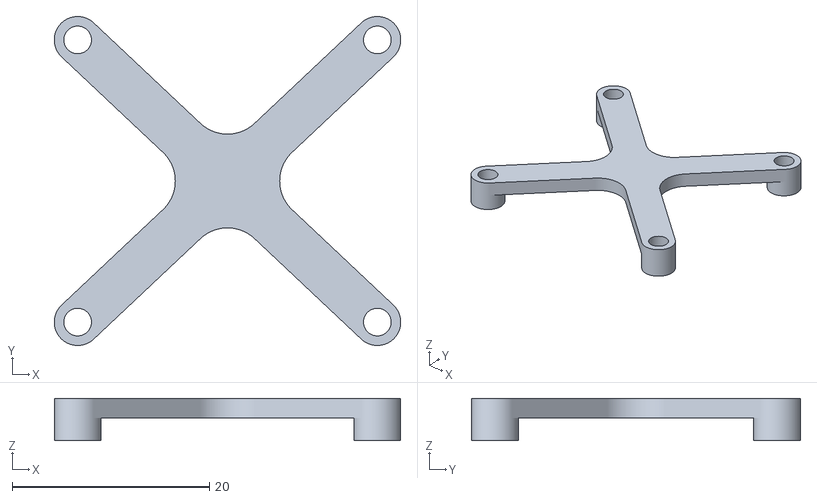
[picture p98: CAD file, 2023-01-20]
Expatria/Jog2K_Deluxe/Enclosure/1.3in - Display Retainer.stl
35.1 x 33.4 x 4.30
