Expatria-Technologies/Mods-Accessories/Expatria/Jog2K_Base/4mm_button_x2.STL

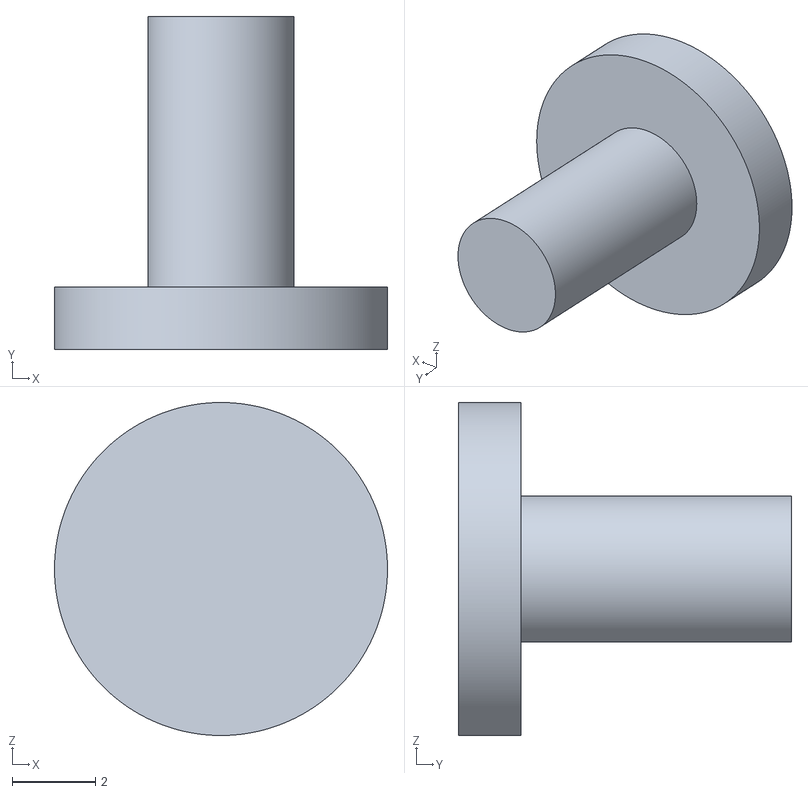
[picture p99: CAD file, 2023-01-20]
Expatria/Jog2K_Base/4mm_button_x2.STL
8.00 x 8.00 x 8.00
