Expatria-Technologies/Mods-Accessories/Expatria/Jog2K_Base/Window.SLDPRT

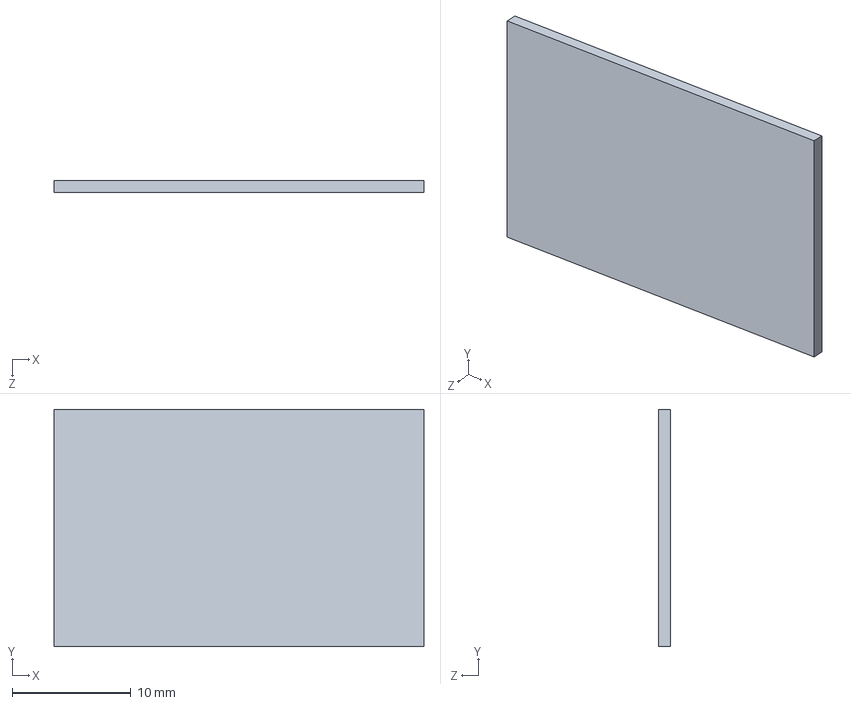
[picture p101: CAD file, 2023-01-20]
Expatria/Jog2K_Base/Window.SLDPRT
31.2 x 20.0 x 1.00 mm
