Expatria-Technologies/Mods-Accessories/Expatria/Jog2K_Deluxe/Buttons/Black/Fn Button Cover.stl

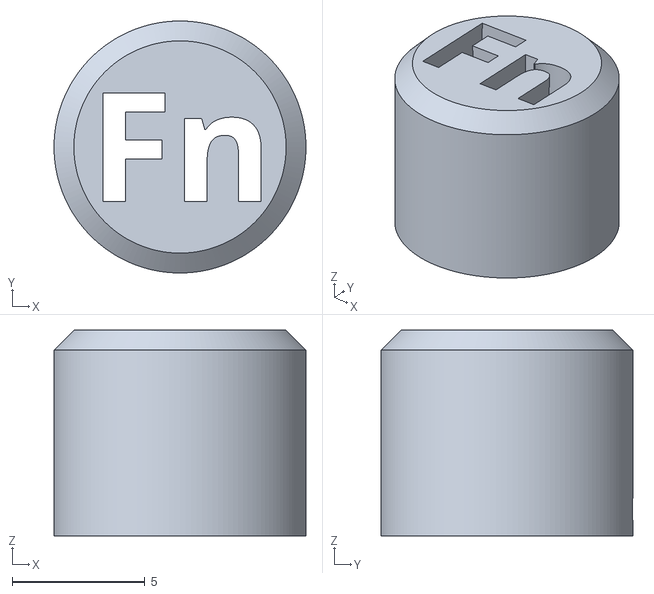
[picture p102: CAD file, 2023-01-20]
Expatria/Jog2K_Deluxe/Buttons/Black/Fn Button Cover.stl
9.50 x 9.50 x 7.75
