Expatria-Technologies/Mods-Accessories/Expatria/Jog2K_Deluxe/Buttons/Black/Raise Button Cover x2.stl

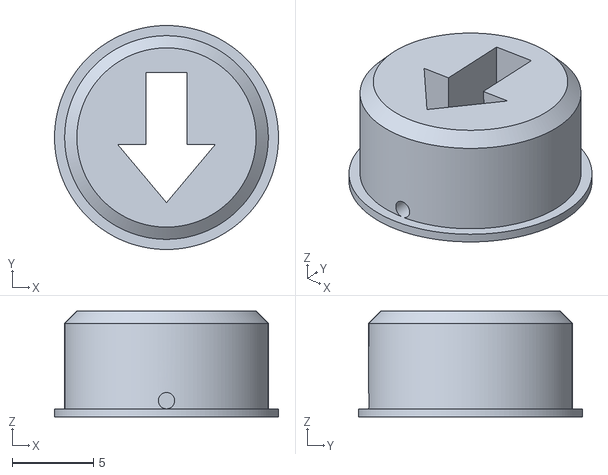
[picture p103: CAD file, 2023-01-20]
Expatria/Jog2K_Deluxe/Buttons/Black/Raise Button Cover x2.stl
13.8 x 13.8 x 6.50
