Expatria-Technologies/Mods-Accessories/Expatria/Jog2K_Deluxe/Buttons/Black/4mm Button Short x2.stl

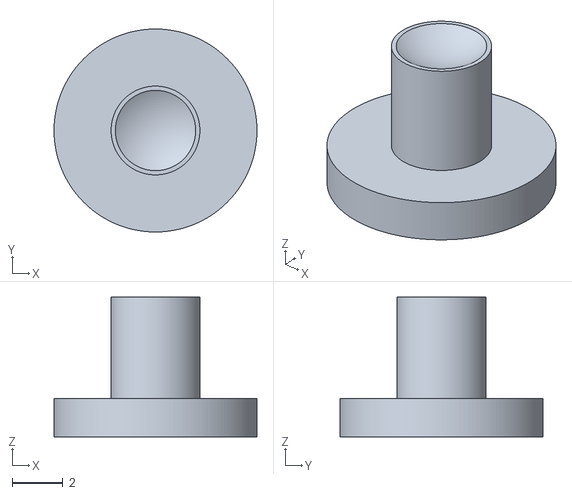
[picture p104: CAD file, 2023-01-20]
Expatria/Jog2K_Deluxe/Buttons/Black/4mm Button Short x2.stl
8.00 x 8.00 x 5.50
